ZayasAnaFlorencia/YararaTeam_WRO_2023/photos & videos/WhatsApp Image 2023-10-11 at 20.48.38 (1) - copia.jpeg

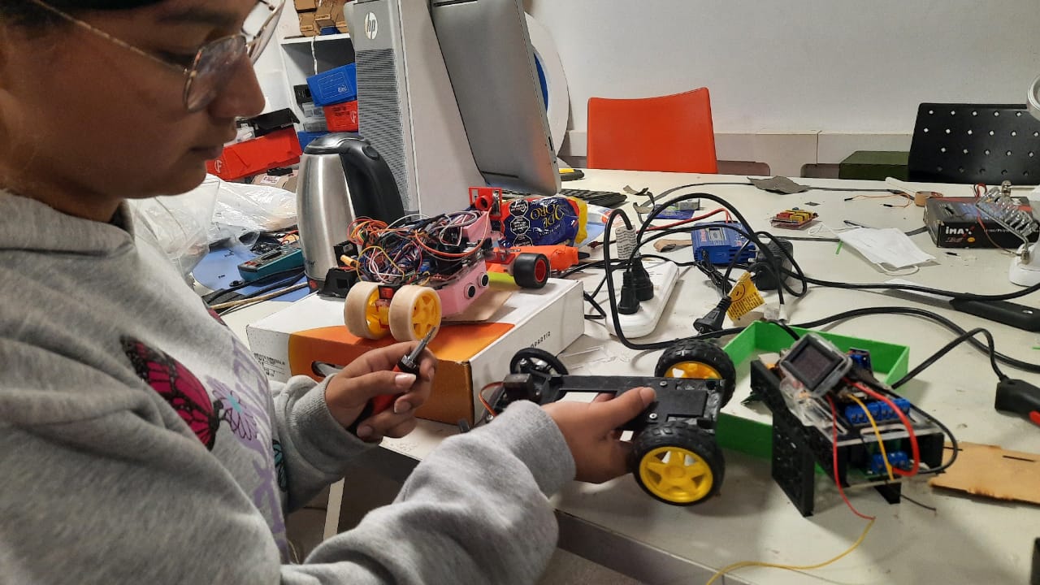
photos & videos/WhatsApp Image 2023-10-11 at 20.48.38 (1) - copia.jpeg
