ZayasAnaFlorencia/YararaTeam_WRO_2023/yararaTeam.v2/photos & videos/WhatsApp Image 2023-10-11 at 20.48.39 (2).jpeg

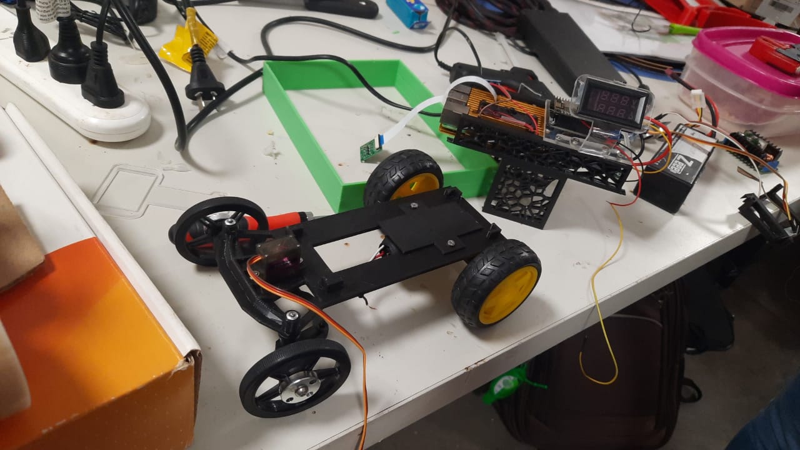
yararaTeam.v2/photos & videos/WhatsApp Image 2023-10-11 at 20.48.39 (2).jpeg
