ZayasAnaFlorencia/YararaTeam_WRO_2023/yararaTeam.v2/photos & videos/WhatsApp Image 2023-10-18 at 15.05.12.jpeg

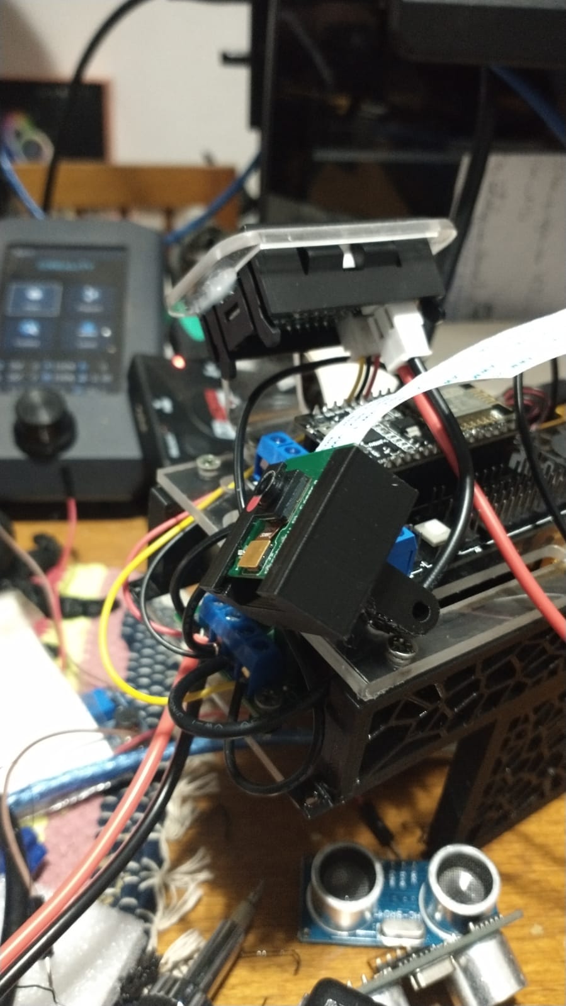
yararaTeam.v2/photos & videos/WhatsApp Image 2023-10-18 at 15.05.12.jpeg
