ZayasAnaFlorencia/YararaTeam_WRO_2023/yararaTeam.v1/chasis/yararaTeam_chasis_v1.stl

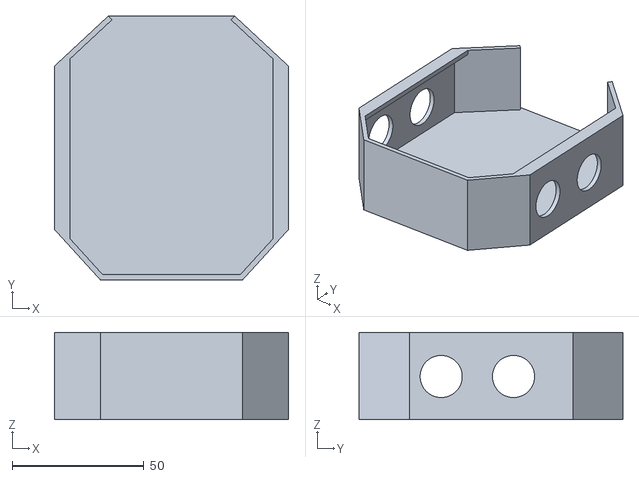
[picture p35: CAD file, 2023-09-29, an earlier design]
yararaTeam.v1/chasis/yararaTeam_chasis_v1.stl
89.0 x 100.3 x 33.2
